William-Yen/AS5600_scale-door-angle-sensors/images/PXL_20240223_013450838.jpg

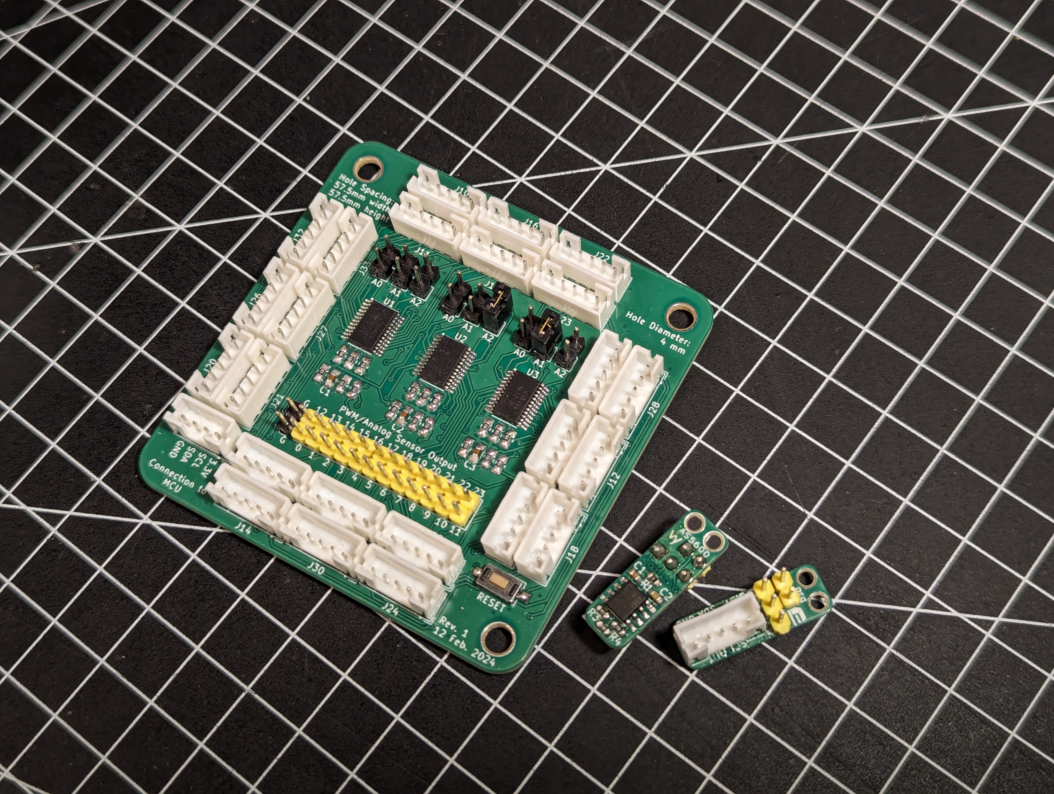
images/PXL_20240223_013450838.jpg
