William-Yen/AS5600_scale-door-angle-sensors/images/PXL_20240223_013846819.jpg

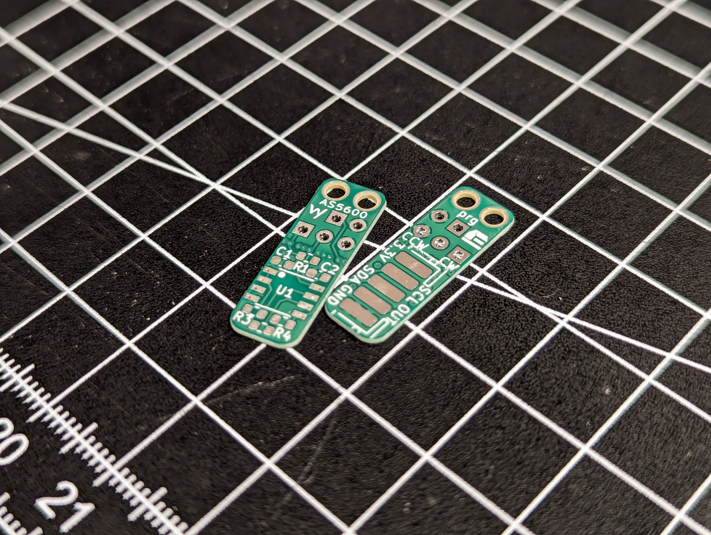
images/PXL_20240223_013846819.jpg
